loscorpione/VFO-BFO-HF-ESP32-Si5351/VFO-BFO HF ESP32 Code/src/modes.h

#ifndef MODES_H
#define MODES_H

enum Mode {
  MODE_AM = 0,   // 00 in binario
  MODE_LSB = 1,  // 01 in binario
  MODE_USB = 2,  // 10 in binario
  MODE_CW = 3,   // 11 in binario
  MODE_COUNT
};

extern const char* modeNames[];
extern int currentMode;

void changeMode();
void updateModeInfo();
void updateBFOForMode();  

#endif
